dodotronix/Haptix/analysis/hw/IMG_20181219_160330.jpg

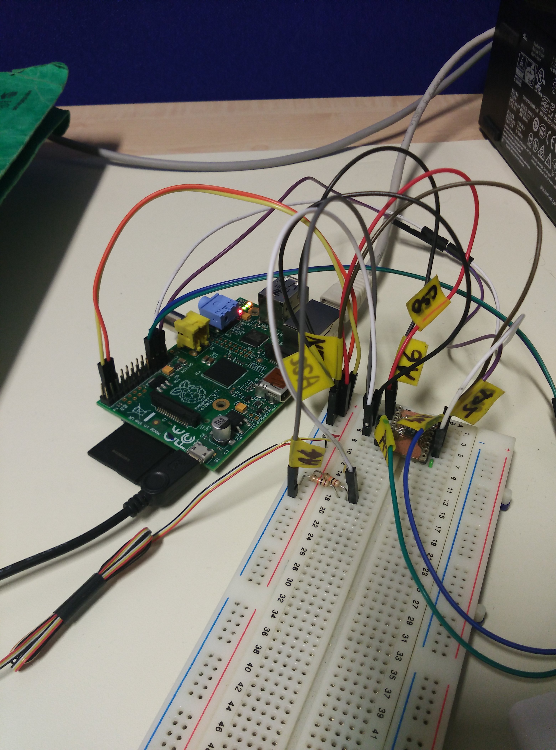
analysis/hw/IMG_20181219_160330.jpg
