dodotronix/Haptix/analysis/hw/IMG_20181219_162428.jpg

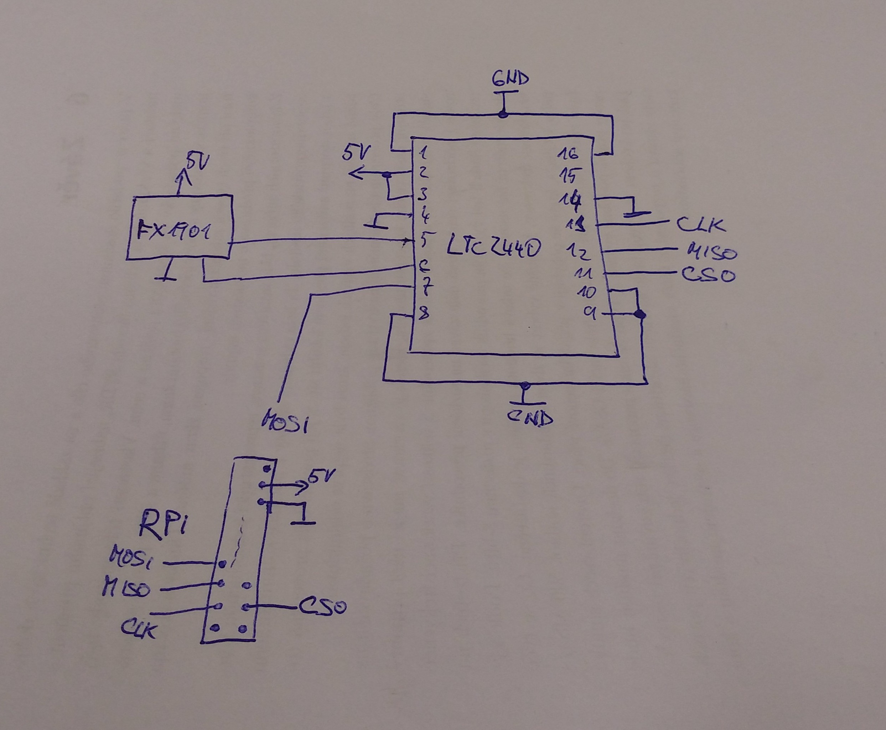
analysis/hw/IMG_20181219_162428.jpg
