dodotronix/Haptix/fw/force_measure.py

#!/usr/bin/python
# -*- coding: utf-8 -*-

import pyvisa

import logging as log
import numpy as np
import matplotlib.pyplot as plot

from math import ceil
from time import sleep
from datetime import datetime

log.basicConfig(format='%(asctime)s %(levelname)s: %(message)s', 
        datefmt='%m/%d/%Y %I:%M:%S %p',level=log.INFO)

def __wait_until_complete():
    return inst.query("*OPC?")

def __start_acquisition():
    inst.write(f"RUN")
    __wait_until_complete()

def __acquisition_complet(inst):
    inst.write(f"TRIG:SWE SING")
    log.info("waiting for the acquisition")
    while inst.query("TRIG:STAT?") != "STOP":
        sleep(0.1)

    return get_wave_data(inst)

def get_wave_data(inst):
    number_of_data = int(inst.query("ACQ:MDEP?"))
    sampling_rate = inst.query("ACQ:SRAT?")
    time_offset = inst.query("TIM:MAIN:OFFS?")
    xorigin = inst.query("WAVeform:XOR?")

    points_per_packet = 24e4
    packets = ceil(number_of_data / points_per_packet)
    log.info(f"packets: {packets}")

    log.info(f"Time offset: {time_offset}")
    log.info(f"X origin: {xorigin}")
    log.info(f"Memory size: {number_of_data}")
    log.info(f"Sampling rate: {sampling_rate}")

    data = np.zeros((number_of_data, 4))

    for ch in range (1, 5):
        inst.write("WAV:MODE RAW")
        inst.write("WAV:FORM BYTE")
        inst.write(f"WAV:SOUR CHAN{ch}")
        __wait_until_complete()

        log.info(f"Downloading from channel {ch}")

        start = 1
        d = b''
        test = np.array([])
        for i in range(packets):
            end = int(start + points_per_packet-1)
            if end > number_of_data:
                end = number_of_data
            log.info(f"start: {start}, end: {end}")
            inst.write(f"WAV:STAR {start}")
            inst.write(f"WAV:STOP {end}")
            inst.write(f"WAV:DATA?")
            start = end + 1
            d = inst.read_raw()
            header_length = int(d[1:2])
            num_bytes = int(d[2:2+header_length])
            waveform_data = d[2+header_length:2+header_length+num_bytes]
            waveform_array = np.frombuffer(waveform_data, dtype=np.uint8)
            test = np.append(test, waveform_array)

        data[:,ch-1] = test

    return data

def setup(inst, amp, timescale, memsize, trig):

    inst.write_termination = '\n'
    inst.read_termination = '\n'
    inst.timeout = None

    inst.write("*RST")
    __wait_until_complete()

    inst.write("CHAN1:DISP ON")
    inst.write("CHAN2:DISP ON")
    inst.write("CHAN3:DISP ON")
    inst.write("CHAN4:DISP ON")
    __wait_until_complete()

    inst.write("CHAN1:PROB 1")
    inst.write("CHAN2:PROB 1")
    inst.write("CHAN3:PROB 1")
    inst.write("CHAN4:PROB 1")
    __wait_until_complete()

    inst.write(f"CHAN1:SCAL {amp/4}") # vertical - 8 grid parts
    inst.write(f"CHAN2:SCAL {amp/20}") # vertical - 8 grid parts
    inst.write(f"CHAN3:SCAL {amp/20}") # vertical - 8 grid parts
    inst.write(f"CHAN4:SCAL {amp/20}") # vertical - 8 grid parts
    __wait_until_complete()

    inst.write(f"TIM:MAIN:SCAL {timescale}") # time in ms
    __wait_until_complete()
    inst.write(f"TIM:MAIN:OFFS {6*timescale}") # shift zero point left
    __wait_until_complete()

    inst.write(f"ACQ:MDEP {memsize}")
    inst.write(f"CHAN1:OFFS {2*amp/4}")
    inst.write(f"CHAN2:OFFS {amp/20}")
    inst.write(f"CHAN3:OFFS {amp/20}") 
    inst.write(f"CHAN4:OFFS {amp/20}")
    __wait_until_complete()

    inst.write(f"TRIG:EDG:SOUR CHAN4") # trigger source
    inst.write(f"TRIG:EDG:LEV {trig}") # trigger level
    inst.write(f"TRIG:EDG:SLOP POS") # rising edge
    __wait_until_complete()


def close(inst):
    inst.close()

if __name__ == '__main__':
    # memory size is defined by the rigol datasheet
    memdepths = [3000, 30000, 300000, 3000000, 6000000]

    rigol_addr = "10.0.0.14"
    pyvisa_addr = f"TCPIP0::{rigol_addr}::INSTR"
    rm = pyvisa.ResourceManager()
    inst = rm.open_resource(pyvisa_addr)

    log.info(f"Connected to: {inst.query("*IDN?")}")

    # 12 V amplitude 
    # 0.2 s/timescale
    # memory size
    # 1.5 V trigger 
    setup(inst, 0.8, 0.5, memdepths[2], 1.5)
    log.info("Start program")

    try:
        while True:
            __start_acquisition()
            log.info(f"{inst.query('TRIG:STAT?')}")

            force = __acquisition_complet(inst)
            a = f"force_{datetime.now().strftime('%H%M%S')}"
            log.info(f"Saving data to: {a} of length {len(force)}")
            np.savetxt(f'{a}.txt', force, fmt='%.5f')
            log.info("Done")

            # preview
            plot.plot(force[:,0])
            plot.plot(force[:,1])
            plot.plot(force[:,2])
            plot.plot(force[:,3])
            plot.title("Channel samples [-]")
            plot.ylabel("Amplitude [-]")
            plot.grid()
            plot.show()

    except KeyboardInterrupt:
        close(inst)
        log.info("Closed")
